chipperdoodles/SydKey/img/pcbmounttop.jpg

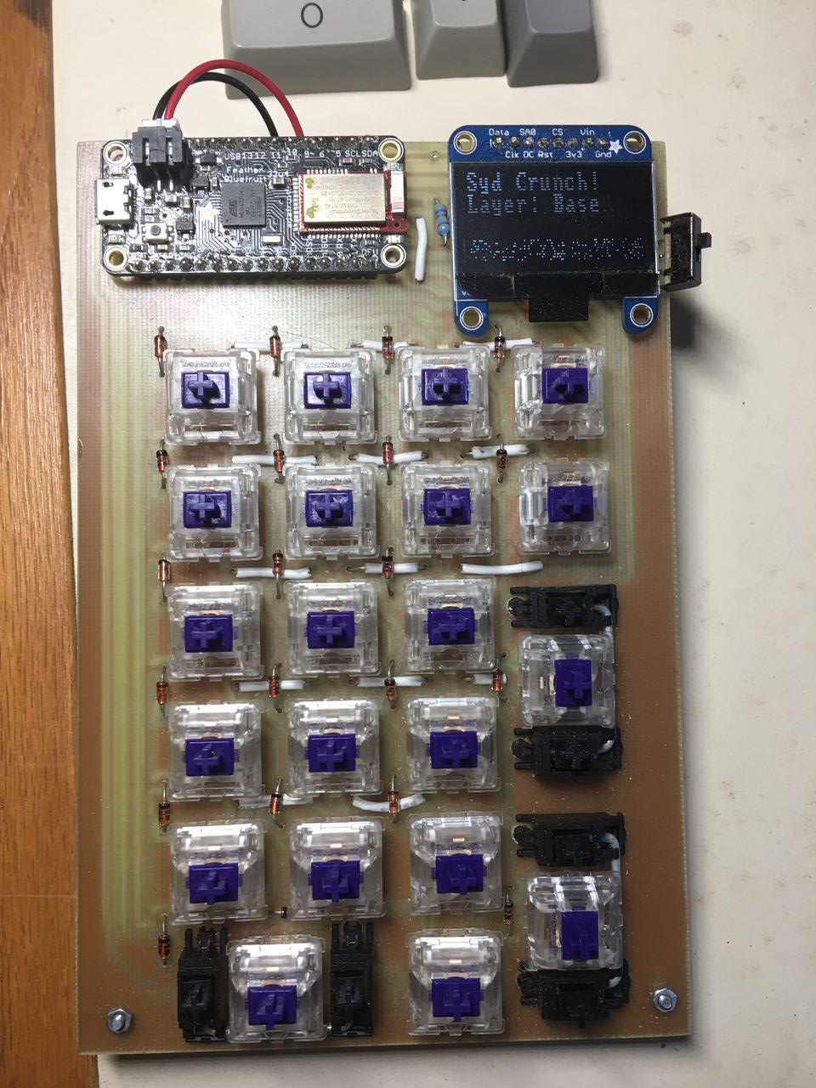
img/pcbmounttop.jpg
